Gouty/Prism_Keyboard/images/photos/IMG_20191020_142423.jpg

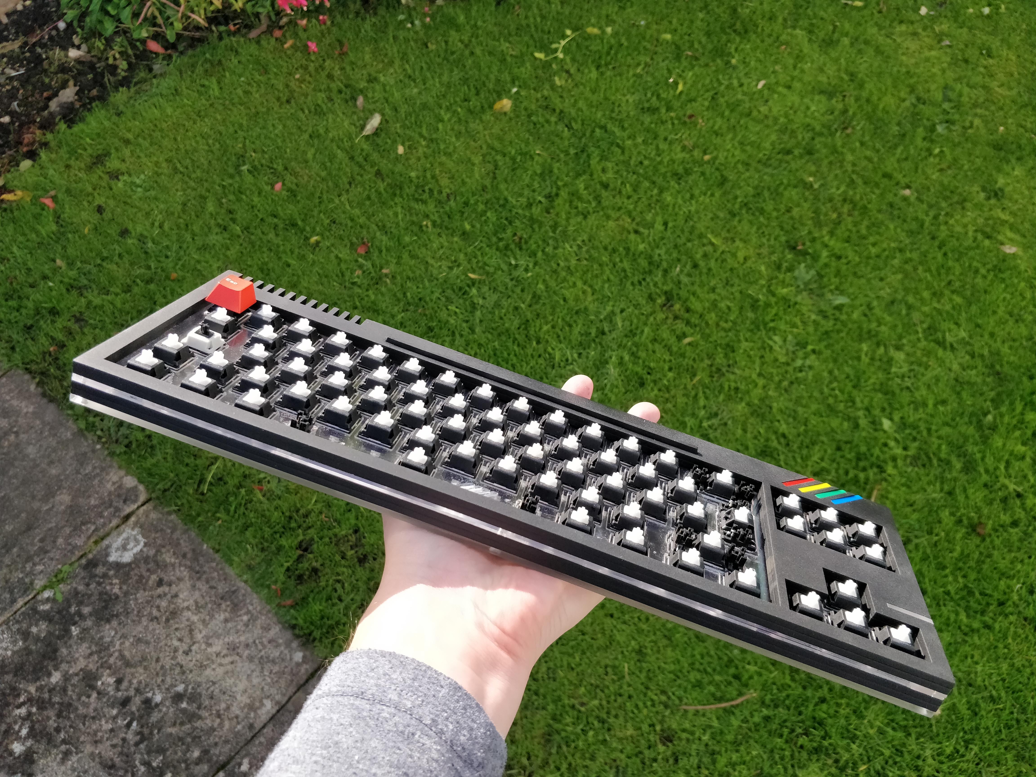
images/photos/IMG_20191020_142423.jpg
