Gouty/Prism_Keyboard/images/photos/IMG_20191020_142458.jpg

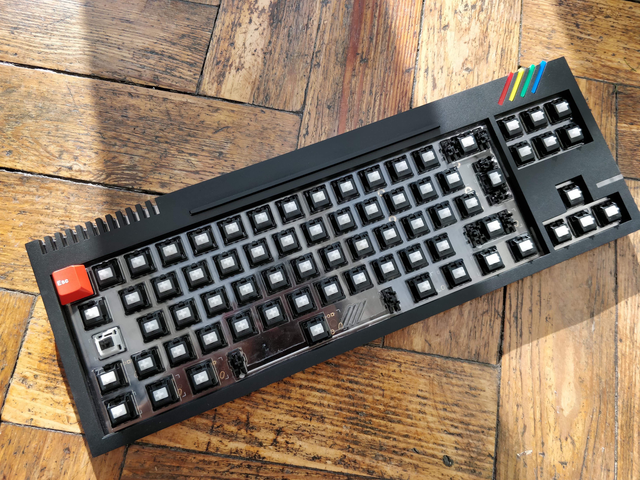
images/photos/IMG_20191020_142458.jpg
