Gouty/Prism_Keyboard/images/photos/IMG_20191026_125048.jpg

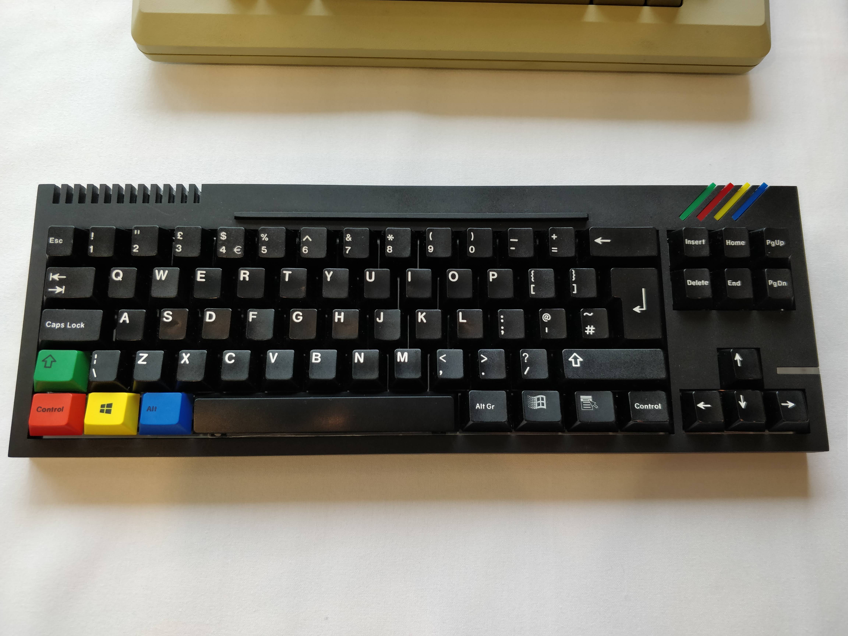
images/photos/IMG_20191026_125048.jpg
