Gouty/Prism_Keyboard/images/photos/IMG_20191102_150124.jpg

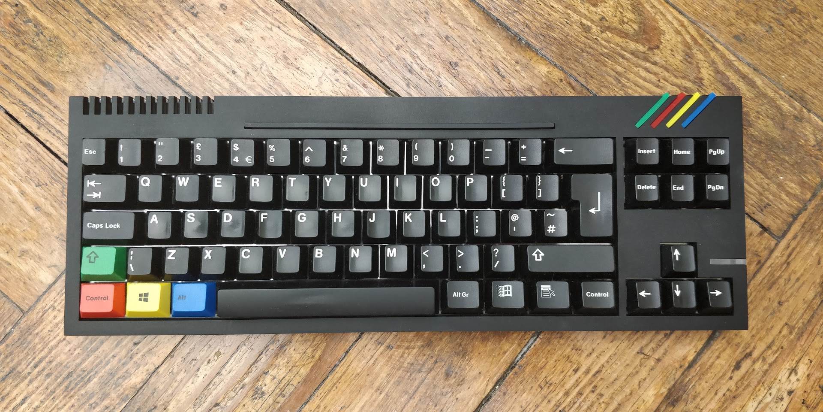
images/photos/IMG_20191102_150124.jpg
