Gouty/Prism_Keyboard/images/photos/IMG_20191102_150212.jpg

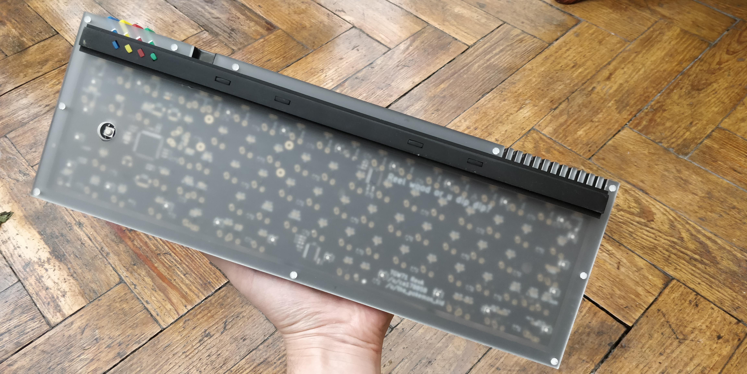
images/photos/IMG_20191102_150212.jpg
