Gouty/Prism_Keyboard/case/RAW/Colour Holder outer.dxf

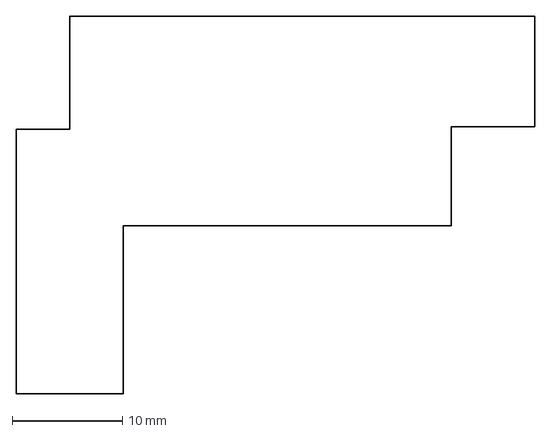
[picture p29: CAD file, 2019-12-20]
case/RAW/Colour Holder outer.dxf
47.0 x 34.2 mm
