Gouty/Prism_Keyboard/case/RAW/Colour Holder inner.dxf

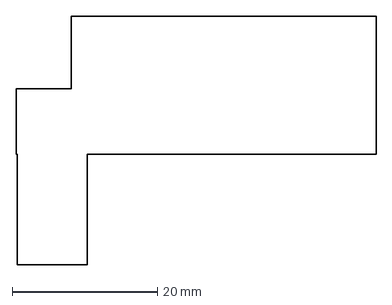
[picture p30: CAD file, 2019-12-20]
case/RAW/Colour Holder inner.dxf
49.6 x 34.2 mm
