Gouty/Prism_Keyboard/case/RAW/Top foot.dxf

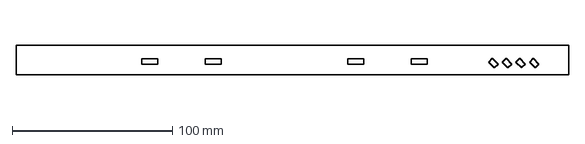
[picture p31: CAD file, 2019-12-20]
case/RAW/Top foot.dxf
345.1 x 18.3 mm
