Gouty/Prism_Keyboard/case/RAW/Light Pipe.dxf

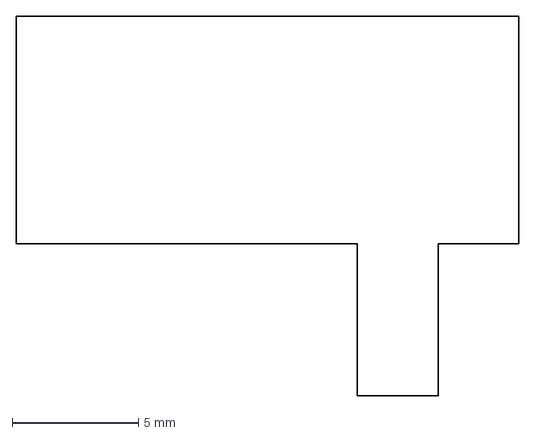
[picture p32: CAD file, 2019-12-20]
case/RAW/Light Pipe.dxf
19.9 x 15.0 mm
